Incomprehensible/Mad_RetroClock/software/main/time_keeper.c

#include "time_keeper.h"
#include "esp_wifi.h"
#include "esp_event.h"
#include "freertos/event_groups.h"
#include "esp_log.h"

// DBG
#ifndef INET6_ADDRSTRLEN
#define INET6_ADDRSTRLEN 48
#endif

/* The event group allows multiple bits for each event, but we only care about two events:
 * - we are connected to the AP with an IP
 * - we failed to connect after the maximum amount of retries */
#define WIFI_CONNECTED_BIT  BIT0
#define WIFI_FAIL_BIT       BIT1
#define AP_MAX_CONN         10

static const char *WIFI = "wifi station";
#define WIFI_SSID "HUAWEI-B535-1489"
#define WIFI_PASS "5YA9GF381L0" // don't worry not real :P
#define WIFI_MAX_RETRY 5

EventGroupHandle_t s_wifi_event_group;

static const char *TAG = "wifi station";

static int s_retry_num = 0;


static void event_handler(void* arg, esp_event_base_t event_base,
                                int32_t event_id, void* event_data)
{
    if (event_base == WIFI_EVENT && event_id == WIFI_EVENT_STA_START) {
        esp_wifi_connect();
    } else if (event_base == WIFI_EVENT && event_id == WIFI_EVENT_STA_DISCONNECTED) {
        if (s_retry_num < WIFI_MAX_RETRY) {
            esp_wifi_connect();
            s_retry_num++;
            ESP_LOGI(WIFI, "retry to connect to the AP");
        } else {
            xEventGroupSetBits(s_wifi_event_group, WIFI_FAIL_BIT);
        }
        ESP_LOGI(WIFI,"connect to the AP fail");
    } else if (event_base == IP_EVENT && event_id == IP_EVENT_STA_GOT_IP) {
        ip_event_got_ip_t* event = (ip_event_got_ip_t*) event_data;
        ESP_LOGI(WIFI, "got ip:" IPSTR, IP2STR(&event->ip_info.ip));
        s_retry_num = 0;
        xEventGroupSetBits(s_wifi_event_group, WIFI_CONNECTED_BIT);
    }
}

bool ntp_set_time(time_t *now)
{
    int retry = 0;
    while (sntp_get_sync_status() == SNTP_SYNC_STATUS_RESET && ++retry < NTP_RETRY_COUNT) {
        ESP_LOGI(TAG, "Waiting for system time to be set... (%d/%d)", retry, NTP_RETRY_COUNT);
        vTaskDelay(1000 / portTICK_PERIOD_MS);
    }
    if (retry == NTP_RETRY_COUNT)
    {
        ESP_LOGE(WIFI, "Couldn't request time through NTP.");
        return false;
    }
    time(now);
    return true;
}

bool wifi_init_sta(time_t *now)
{
    bool status = true;
    s_wifi_event_group = xEventGroupCreate();

    ESP_ERROR_CHECK(esp_netif_init());

    ESP_ERROR_CHECK(esp_event_loop_create_default());
    esp_netif_create_default_wifi_sta();

    wifi_init_config_t cfg = WIFI_INIT_CONFIG_DEFAULT();
    ESP_ERROR_CHECK(esp_wifi_init(&cfg));

    esp_event_handler_instance_t instance_any_id;
    esp_event_handler_instance_t instance_got_ip;
    ESP_ERROR_CHECK(esp_event_handler_instance_register(WIFI_EVENT,
                                                        ESP_EVENT_ANY_ID,
                                                        &event_handler,
                                                        NULL,
                                                        &instance_any_id));
    ESP_ERROR_CHECK(esp_event_handler_instance_register(IP_EVENT,
                                                        IP_EVENT_STA_GOT_IP,
                                                        &event_handler,
                                                        NULL,
                                                        &instance_got_ip));

    wifi_config_t wifi_config = {
        .sta = {
            .ssid = WIFI_SSID,
            .password = WIFI_PASS,
            /* Authmode threshold resets to WPA2 as default if password matches WPA2 standards (pasword len => 8).
             * If you want to connect the device to deprecated WEP/WPA networks, Please set the threshold value
             * to WIFI_AUTH_WEP/WIFI_AUTH_WPA_PSK and set the password with length and format matching to
	     * WIFI_AUTH_WEP/WIFI_AUTH_WPA_PSK standards.
             */
            .threshold = {.authmode = WIFI_AUTH_WPA2_PSK},
        },
    };
    ESP_ERROR_CHECK(esp_wifi_set_mode(WIFI_MODE_STA) );
    ESP_ERROR_CHECK(esp_wifi_set_config(WIFI_IF_STA, &wifi_config) );
    ESP_ERROR_CHECK(esp_wifi_start() );

    ESP_LOGI(TAG, "wifi_init_sta finished.");

    /* Waiting until either the connection is established (WIFI_CONNECTED_BIT) or connection failed for the maximum
     * number of re-tries (WIFI_FAIL_BIT). The bits are set by event_handler() (see above) */
    EventBits_t bits = xEventGroupWaitBits(s_wifi_event_group,
            WIFI_CONNECTED_BIT | WIFI_FAIL_BIT,
            pdFALSE,
            pdFALSE,
            portMAX_DELAY);

    /* xEventGroupWaitBits() returns the bits before the call returned, hence we can test which event actually
     * happened. */
    if (bits & WIFI_CONNECTED_BIT) {
        ESP_LOGI(WIFI, "connected to ap SSID:%s password:%s",
                 WIFI_SSID, WIFI_PASS);
        status = true;
    } else if (bits & WIFI_FAIL_BIT) {
        ESP_LOGI(WIFI, "Failed to connect to SSID:%s, password:%s",
                 WIFI_SSID, WIFI_PASS);
    } else {
        ESP_LOGE(WIFI, "UNEXPECTED EVENT");
    }

    // wait for time to be set
    if (status)
    {
        if (!ntp_set_time(now))
            status = false;
        else
            status = true;
    }

    ESP_ERROR_CHECK(esp_wifi_stop());
    /* The event will not be processed after unregister */
    ESP_ERROR_CHECK(esp_event_handler_instance_unregister(IP_EVENT, IP_EVENT_STA_GOT_IP, instance_got_ip));
    ESP_ERROR_CHECK(esp_event_handler_instance_unregister(WIFI_EVENT, ESP_EVENT_ANY_ID, instance_any_id));
    vEventGroupDelete(s_wifi_event_group);
    return status;
}

static void init_sntp(void)
{
    ESP_LOGI(TAG, "Initializing SNTP");
    sntp_setoperatingmode(SNTP_OPMODE_POLL);
/*
 * If 'NTP over DHCP' is enabled, we set dynamic pool address
 * as a 'secondary' server. It will act as a fallback server in case that address
 * provided via NTP over DHCP is not accessible
 */
    sntp_setservername(0, TIME_SERVER);
    if (SNTP_MAX_SERVERS > 0)
        sntp_setservername(1, TIME_SERVER1);
    // sntp_set_time_sync_notification_cb(time_sync_notification_cb);
    sntp_init();

#ifdef DEBUG
    ESP_LOGI(TAG, "List of configured NTP servers:");

    for (uint8_t i = 0; i < SNTP_MAX_SERVERS; ++i) {
        if (sntp_getservername(i)){
            ESP_LOGI(TAG, "server %d: %s", i, sntp_getservername(i));
        } else {
            // we have either IPv4 or IPv6 address, let's print it
            char buff[INET6_ADDRSTRLEN];
            ip_addr_t const *ip = sntp_getserver(i);
            if (ipaddr_ntoa_r(ip, buff, INET6_ADDRSTRLEN) != NULL)
                ESP_LOGI(TAG, "server %d: %s", i, buff);
        }
    }
#endif
}

bool obtain_time(struct tm *timeinfo)
{
    /**
     * NTP server address could be aquired via DHCP,
     * see following menuconfig options:
     * 'LWIP_DHCP_GET_NTP_SRV' - enable STNP over DHCP
     * 'LWIP_SNTP_DEBUG' - enable debugging messages
     *
     * NOTE: This call should be made BEFORE esp aquires IP address from DHCP,
     * otherwise NTP option would be rejected by default.
     */
    sntp_servermode_dhcp(1);      // accept NTP offers from DHCP server, if any

    init_sntp();

    time_t now = 0;
    if (!wifi_init_sta(&now))
        return false;

    char strftime_buf[64];
    // Set timezone to Moscow
    // setenv("TZ", "MSK-3", 1);
    setenv("TZ", "CET-1CEST,M3.5.0/02,M10.5.0/03", 1);

    tzset();
    localtime_r(&now, timeinfo);
#ifdef DEBUG
    strftime(strftime_buf, sizeof(strftime_buf), "%c", timeinfo);
    ESP_LOGI(TAG, "The current date/time in Moscow is: %s", strftime_buf);
#endif
    return true;
}
