Incomprehensible/Mad_RetroClock/software/main/time_keeper.h

#ifndef TIME_KEEPER_H
#define TIME_KEEPER_H

#include <time.h>
#include <sys/time.h>
#include "esp_sntp.h"

// #define UTC_OFFSET (3 * 60 * 60)
#define TIME_SERVER2 "at.pool.ntp.org"//"0.ru.pool.ntp.org"
#define TIME_SERVER1 "0.at.pool.ntp.org"//"1.ru.pool.ntp.org"
#define TIME_SERVER "pool.ntp.org"

#define NTP_RETRY_COUNT 7

#endif
